geaz/simplyRetro-Z5/images/9.jpg

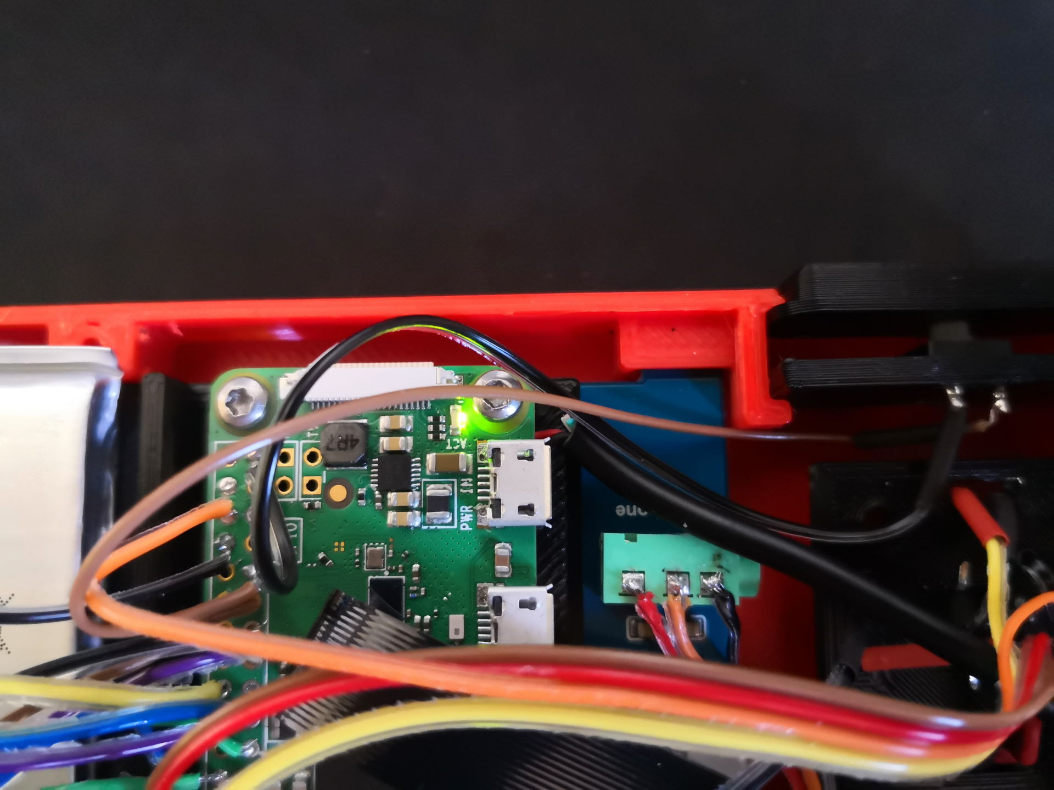
images/9.jpg
