geaz/simplyRetro-Z5/images/10.jpg

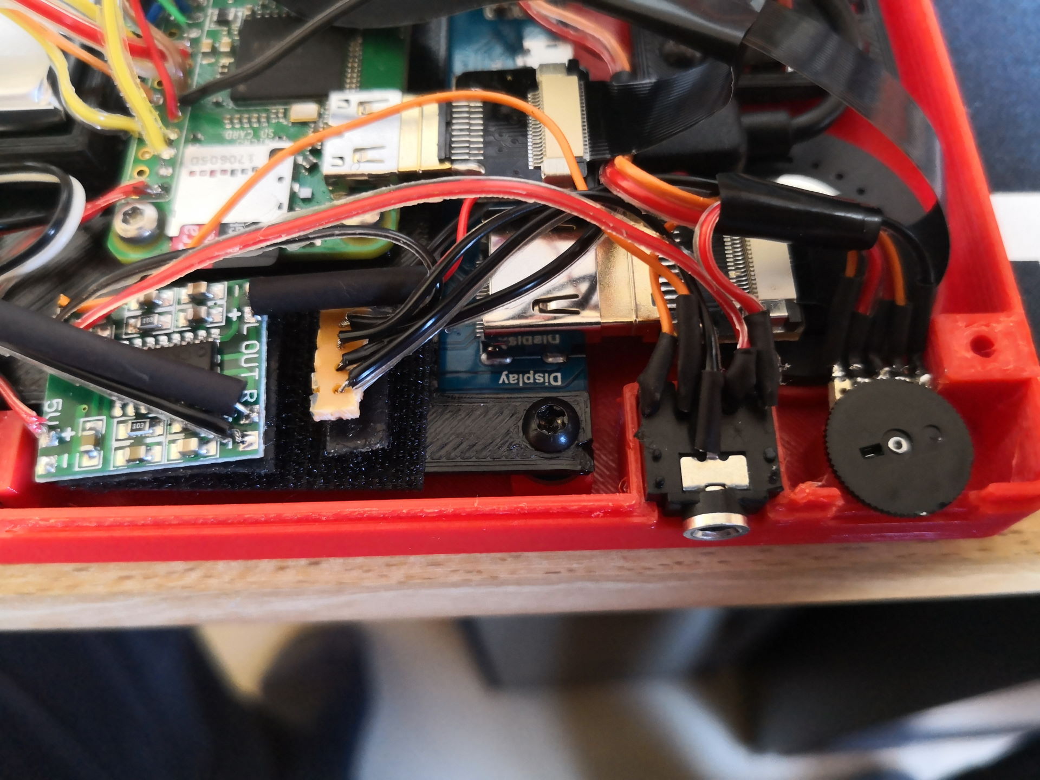
images/10.jpg
