geaz/simplyRetro-Z5/images/11.jpg

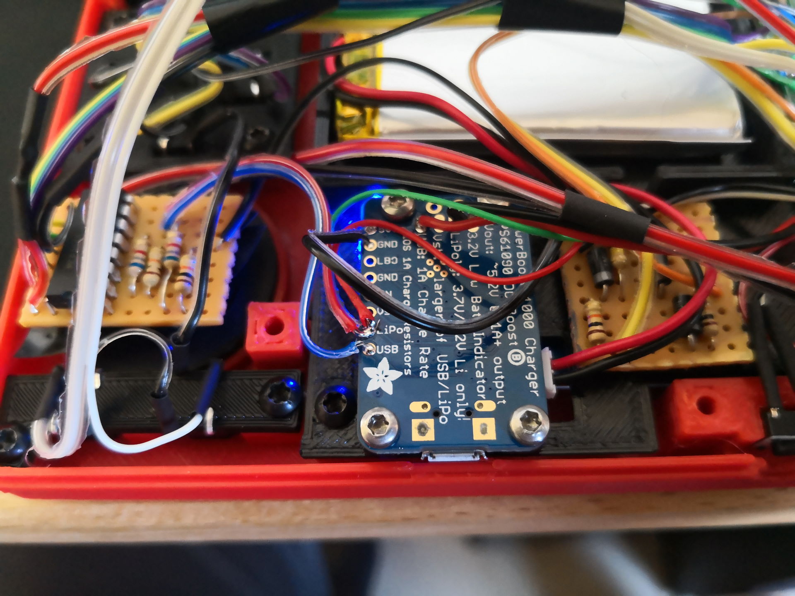
images/11.jpg
