geaz/simplyRetro-Z5/images/12.jpg

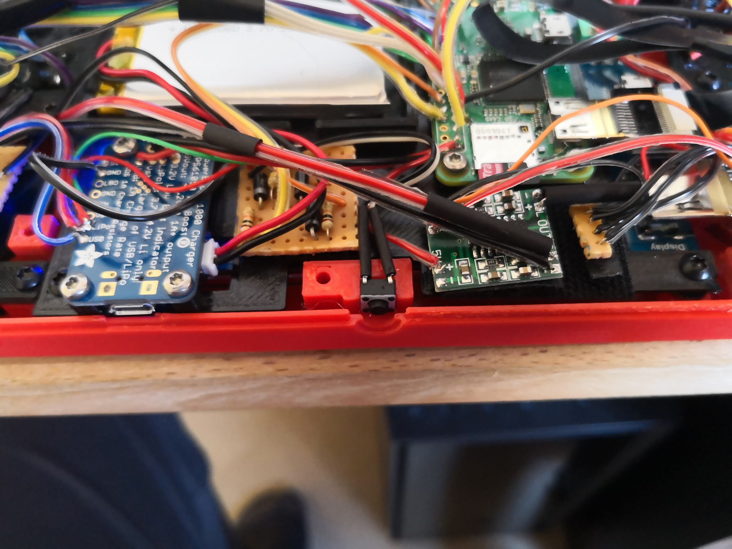
images/12.jpg
