geaz/simplyRetro-Z5/stl/Control Mount C.stl

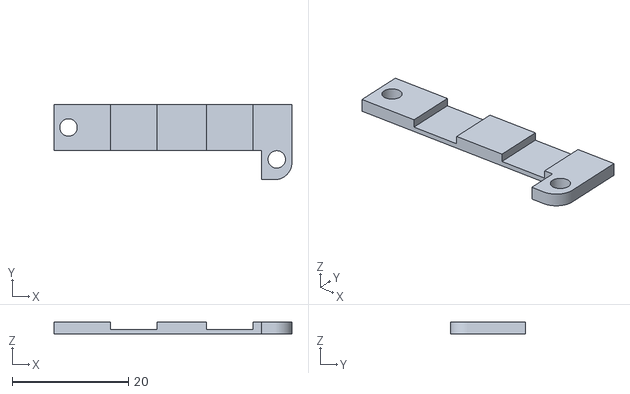
[picture p36: CAD file, 2019-05-29]
stl/Control Mount C.stl
41.0 x 13.0 x 2.00
